wenlinl/shike/media/产品宣传图/3D打印外壳预览/02-背面.png

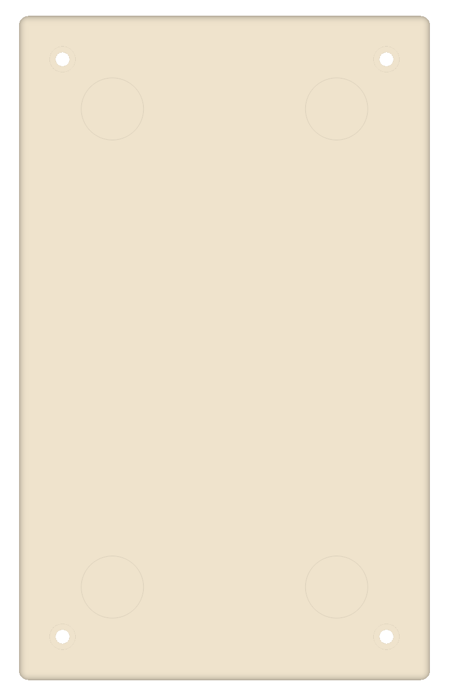
media/产品宣传图/3D打印外壳预览/02-背面.png
