wenlinl/shike/media/产品宣传图/3D打印外壳预览/04-T5开发板-正面.png

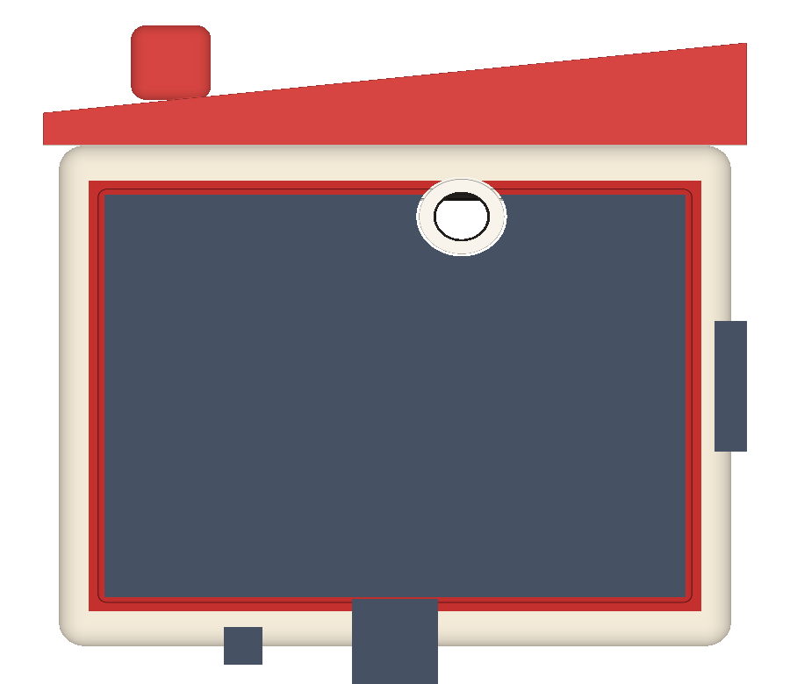
media/产品宣传图/3D打印外壳预览/04-T5开发板-正面.png
