wenlinl/shike/media/产品宣传图/3D打印外壳预览/07-T5开发板-确认图.png

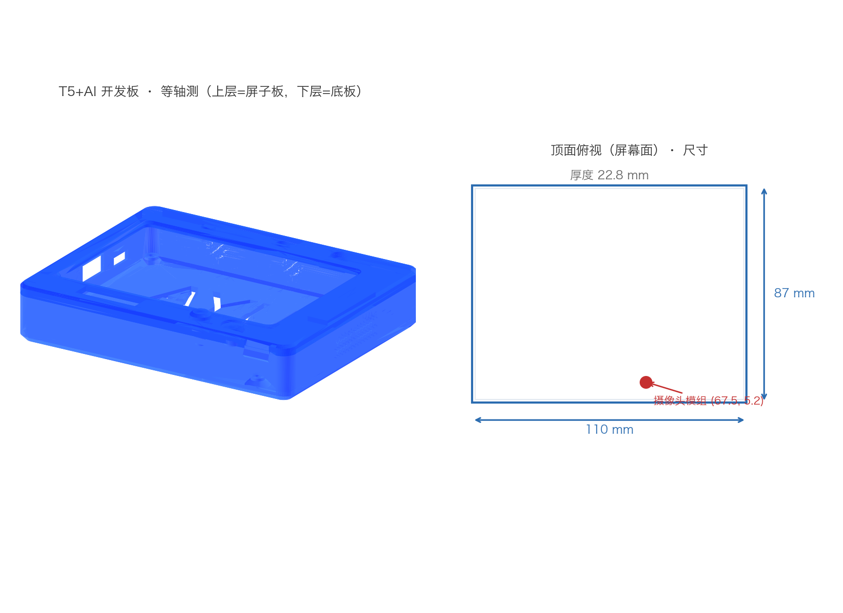
media/产品宣传图/3D打印外壳预览/07-T5开发板-确认图.png
