wenlinl/shike/media/产品宣传图/05-宣传长图-D.jpg

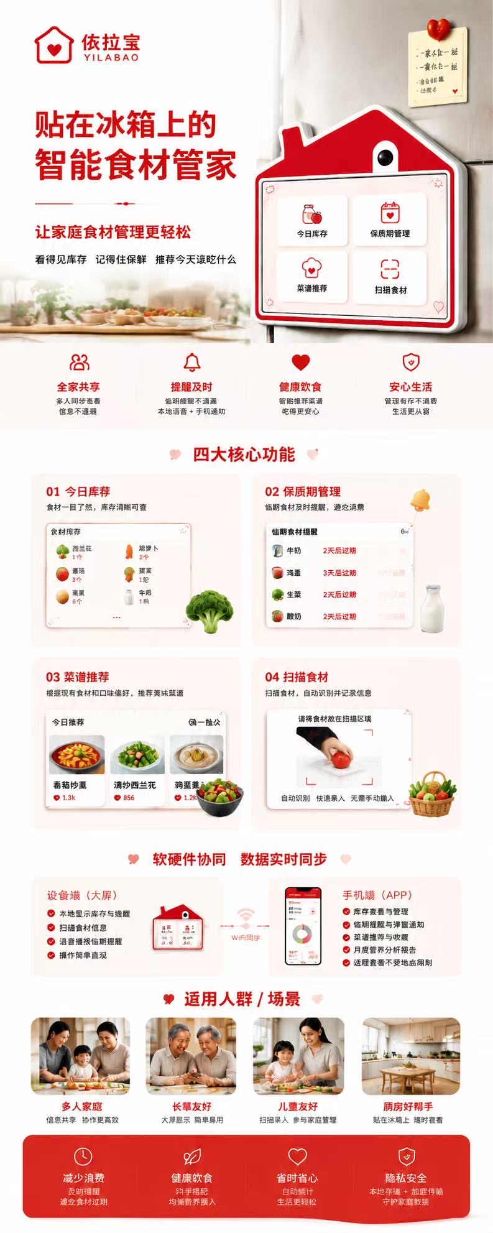
media/产品宣传图/05-宣传长图-D.jpg
