wenlinl/shike/media/产品宣传图/08-在线演示二维码.png

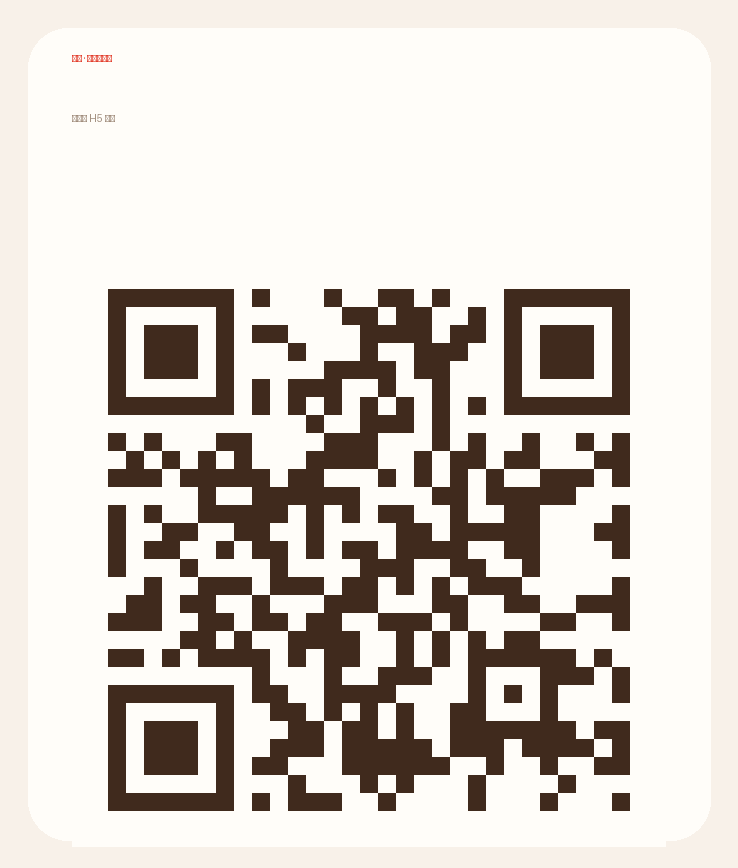
media/产品宣传图/08-在线演示二维码.png
