wenlinl/shike/media/软件示意图/手机APP/01-首页.png

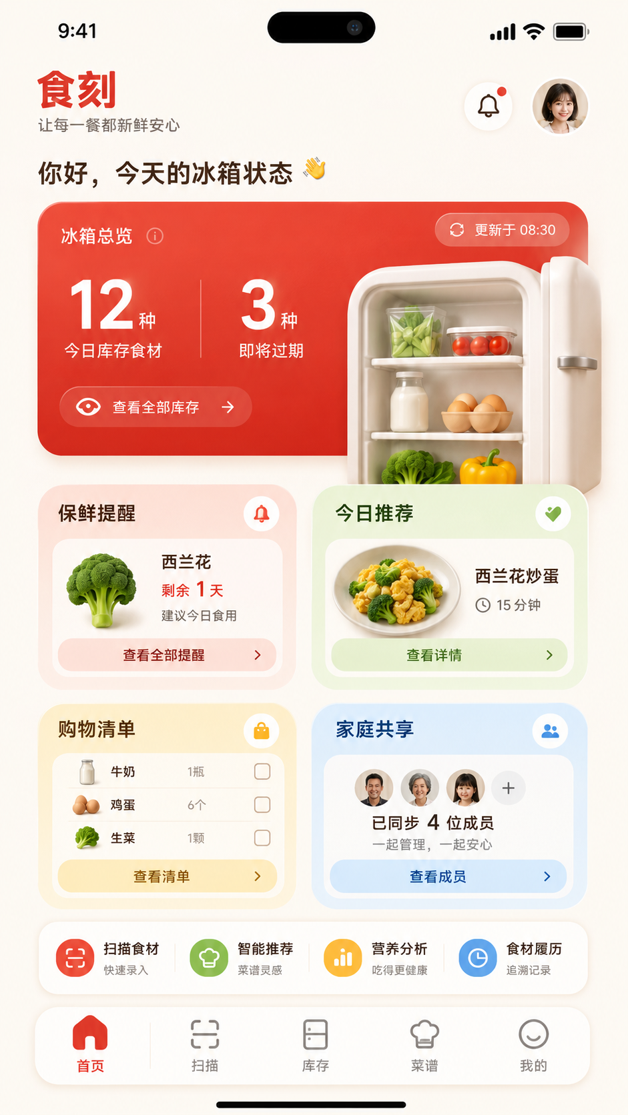
media/软件示意图/手机APP/01-首页.png
