wenlinl/shike/media/软件示意图/手机APP/02-我的库存.png

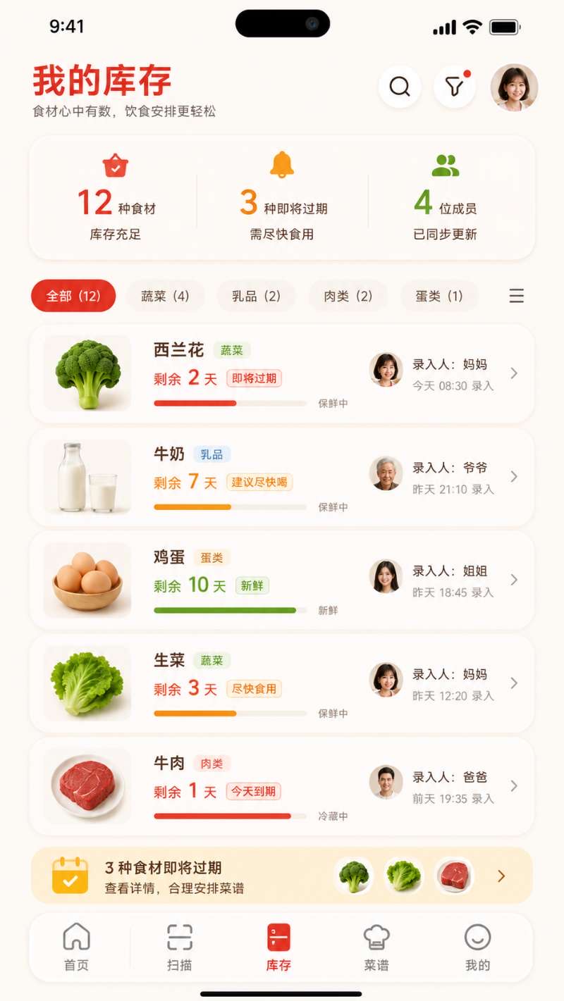
media/软件示意图/手机APP/02-我的库存.png
