wenlinl/shike/media/软件示意图/手机APP/04-营养分析.jpg

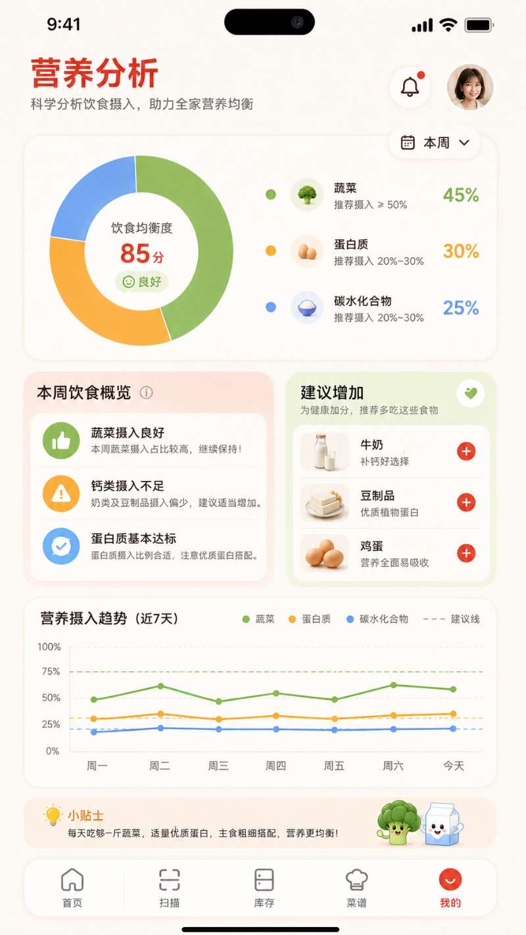
media/软件示意图/手机APP/04-营养分析.jpg
