wenlinl/shike/media/软件示意图/手机APP/05-菜谱推荐.png

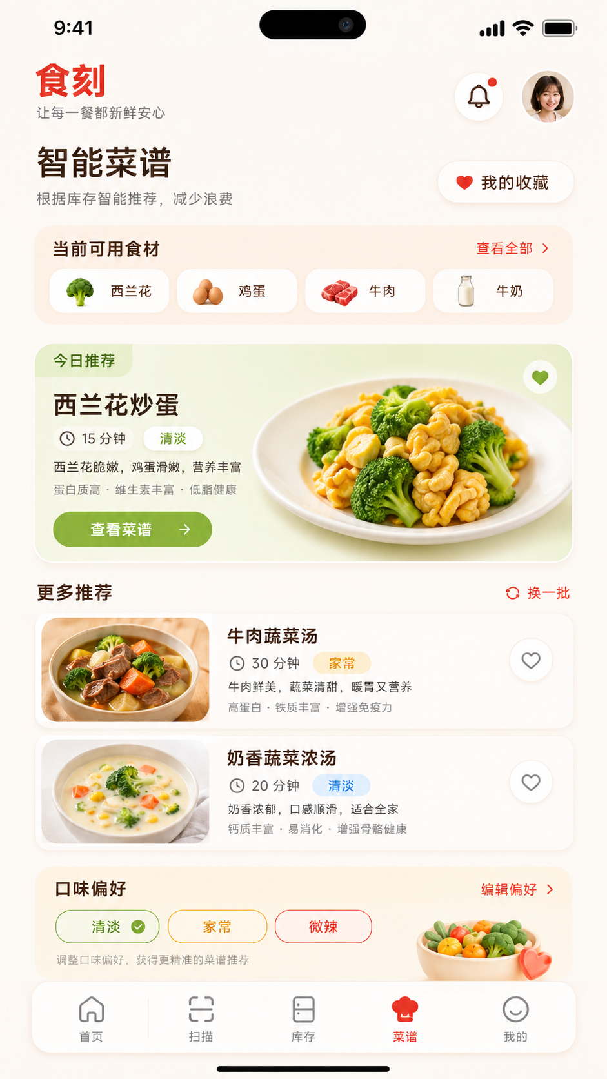
media/软件示意图/手机APP/05-菜谱推荐.png
