wenlinl/shike/media/软件示意图/手机APP/06-扫描识别.jpg

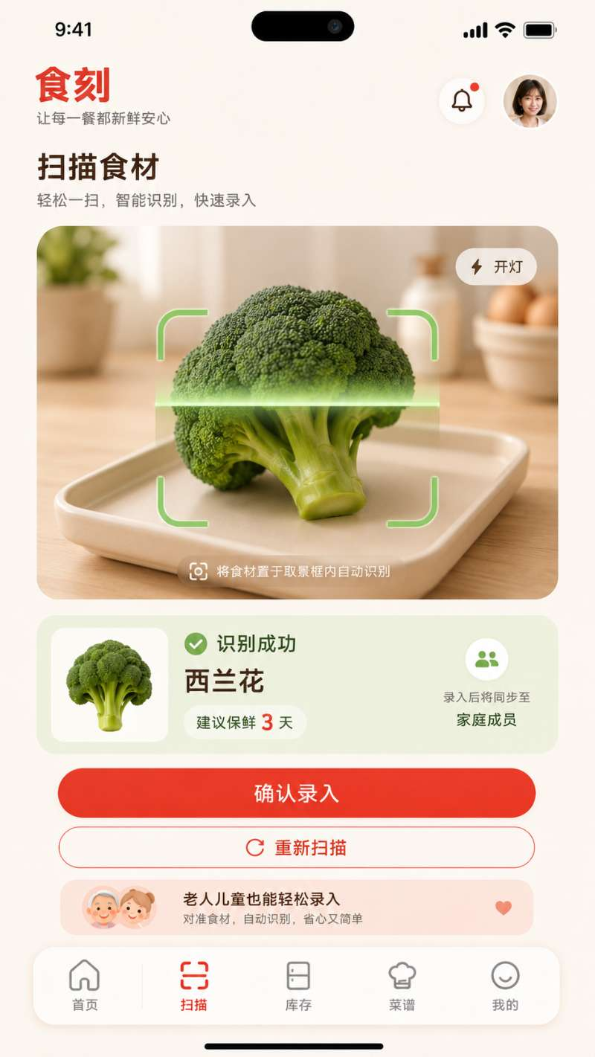
media/软件示意图/手机APP/06-扫描识别.jpg
