wenlinl/shike/media/软件示意图/硬件设备界面/01-待机页.png

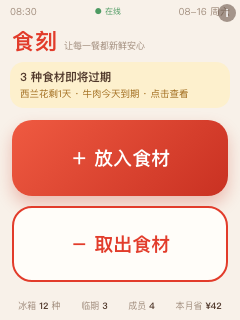
media/软件示意图/硬件设备界面/01-待机页.png
