wenlinl/shike/media/软件示意图/硬件设备界面/02-拍照倒计时.png

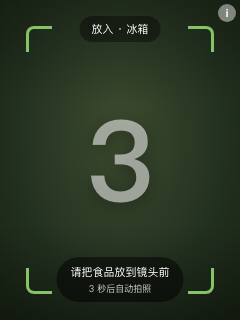
media/软件示意图/硬件设备界面/02-拍照倒计时.png
