wenlinl/shike/media/软件示意图/硬件设备界面/04-识别结果-放入.png

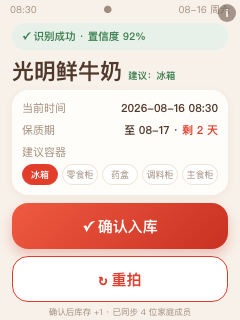
media/软件示意图/硬件设备界面/04-识别结果-放入.png
