wenlinl/shike/media/软件示意图/硬件设备界面/06-识别失败-重拍.png

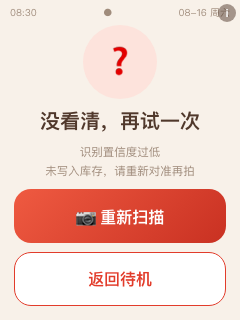
media/软件示意图/硬件设备界面/06-识别失败-重拍.png
