wenlinl/shike/media/软件示意图/硬件设备界面/07-网络错误.png

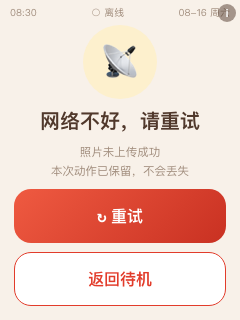
media/软件示意图/硬件设备界面/07-网络错误.png
