wenlinl/shike/media/软件示意图/硬件设备界面/09-启动页.png

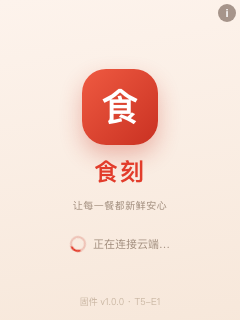
media/软件示意图/硬件设备界面/09-启动页.png
