wenlinl/shike/media/软件示意图/硬件设备界面/10-硬件界面-总览.png

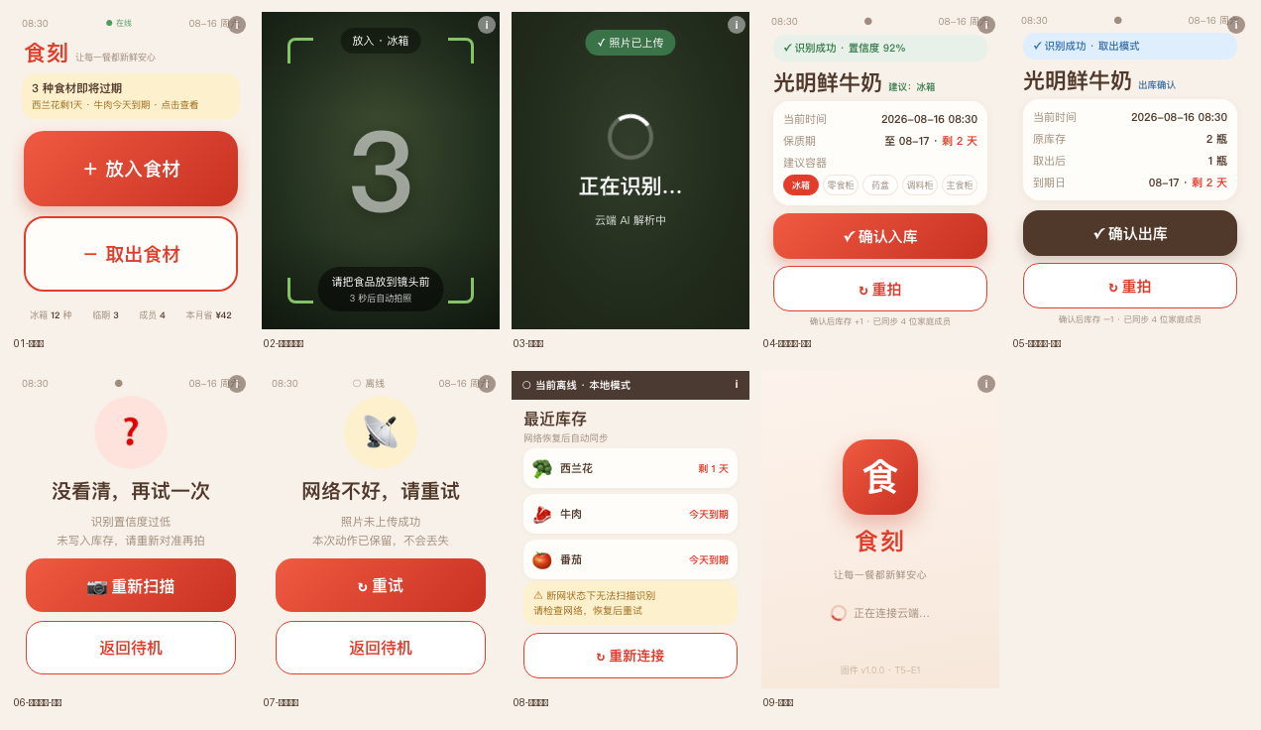
media/软件示意图/硬件设备界面/10-硬件界面-总览.png
