wenlinl/shike/media/产品宣传图/3D打印外壳预览/03-装配图.png

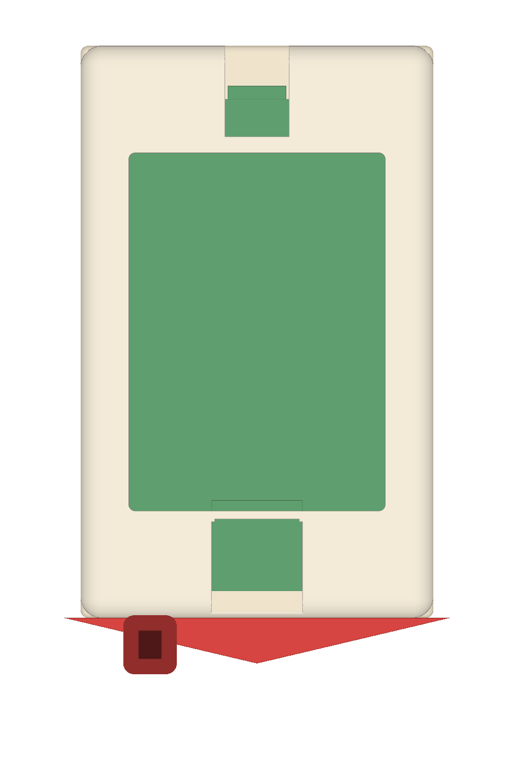
media/产品宣传图/3D打印外壳预览/03-装配图.png
