wenlinl/shike/media/产品宣传图/3D打印外壳预览/06-T5开发板-装配图.png

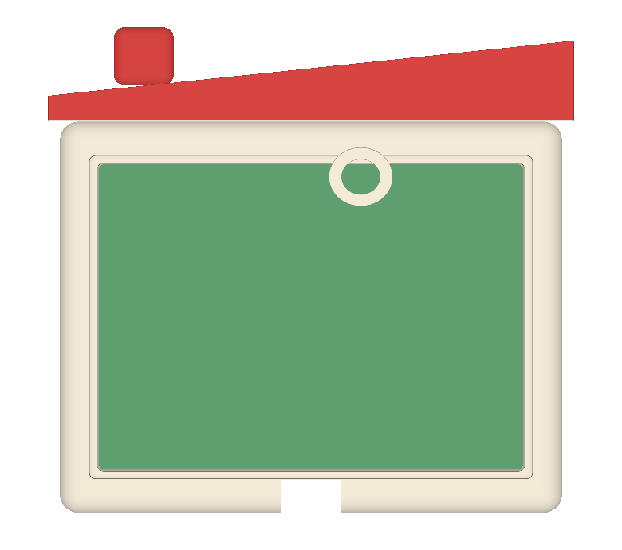
media/产品宣传图/3D打印外壳预览/06-T5开发板-装配图.png
